makbit/MIDI2USB/Firmware/efm8_config.h

/******************************************************************************
 * Copyright (c) 2014 by Silicon Laboratories Inc. All rights reserved.
 *
 * http://developer.silabs.com/legal/version/v11/Silicon_Labs_Software_License_Agreement.txt
 *****************************************************************************/
 
#ifndef __EFM8_CONFIG_H__
#define __EFM8_CONFIG_H__

#endif // __EFM8_CONFIG_H__
